aritmaldzamu/xgio-monorep/backend/api/ruta_ideal_dispersion.png

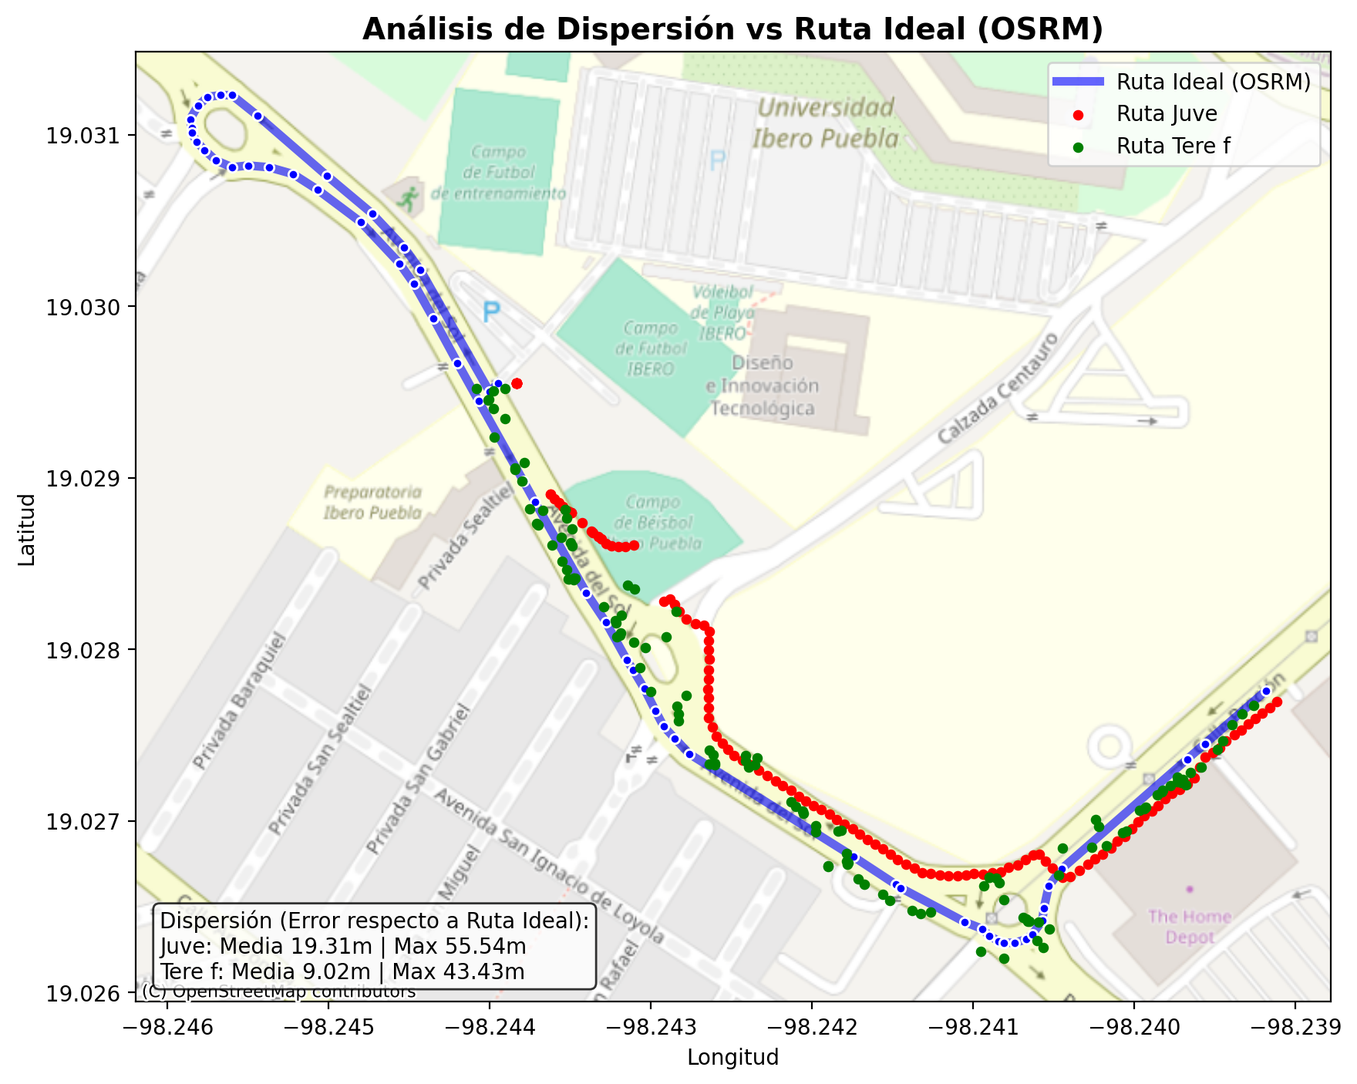
backend/api/ruta_ideal_dispersion.png
