aritmaldzamu/xgio-monorep/backend/api/rutas_juve_tere_landmarks.png

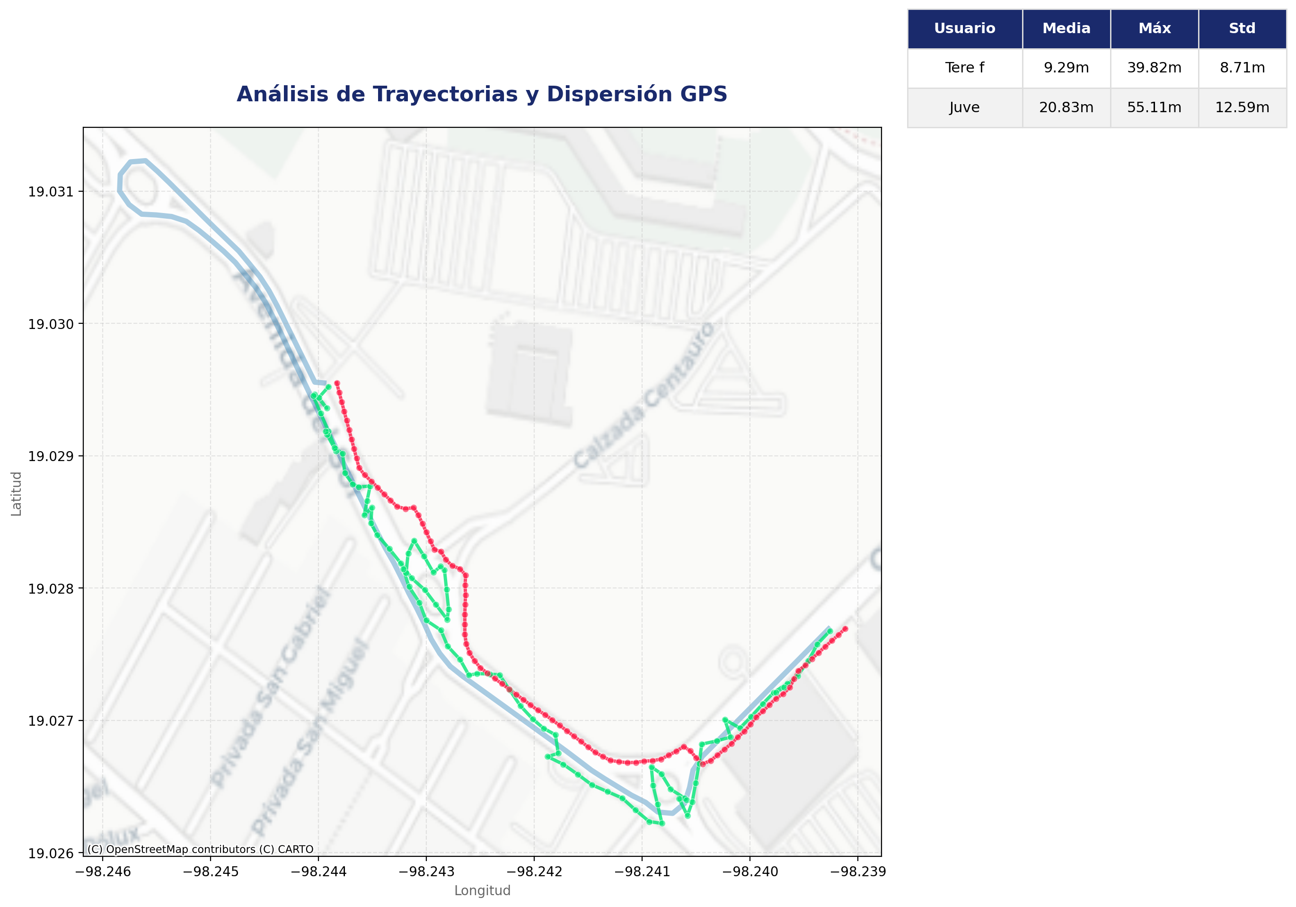
backend/api/rutas_juve_tere_landmarks.png
