aritmaldzamu/xgio-monorep/docs/assets/imagenes/mi_perfil.jpeg

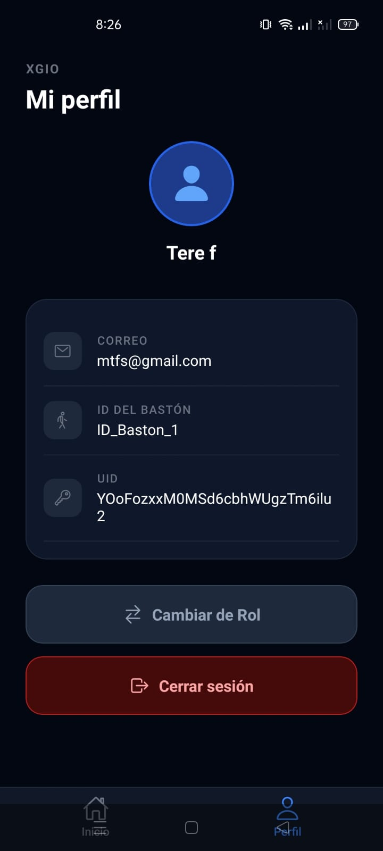
docs/assets/imagenes/mi_perfil.jpeg
