aritmaldzamu/xgio-monorep/tools/qr_output/XGIO-BASTON-1.png

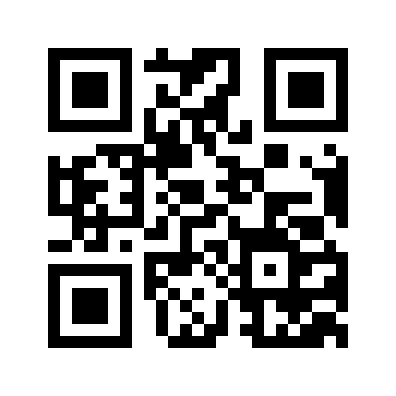
tools/qr_output/XGIO-BASTON-1.png
