aritmaldzamu/xgio-monorep/tools/qr_output/XGIO-BASTON-2.png

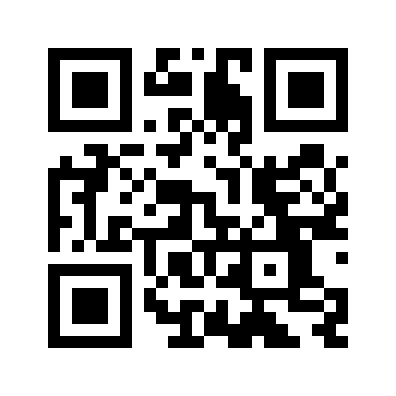
tools/qr_output/XGIO-BASTON-2.png
