aritmaldzamu/xgio-monorep/tools/qr_output/XGIO-BASTON-3.png

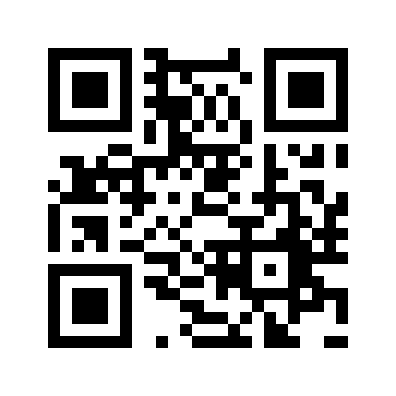
tools/qr_output/XGIO-BASTON-3.png
