aritmaldzamu/xgio-monorep/tools/qr_output/XGIO-BASTON-4.png

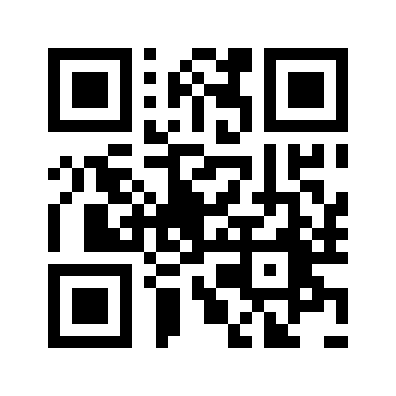
tools/qr_output/XGIO-BASTON-4.png
